ABillBlakely/Silver-Box-Modular-HiFi-Preamp/mcad/Bourns PTV111-4425A.step

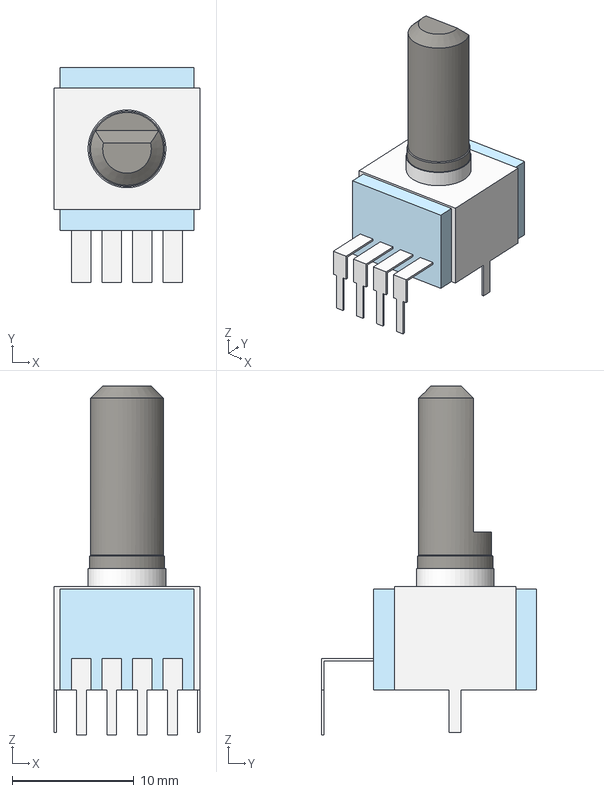
[picture p19: CAD file, 2023-02-01]
mcad/Bourns PTV111-4425A.step
12.0 x 17.7 x 28.7 mm
